Wudker/Weather_station/Hardware/Model/Station/ul.stl

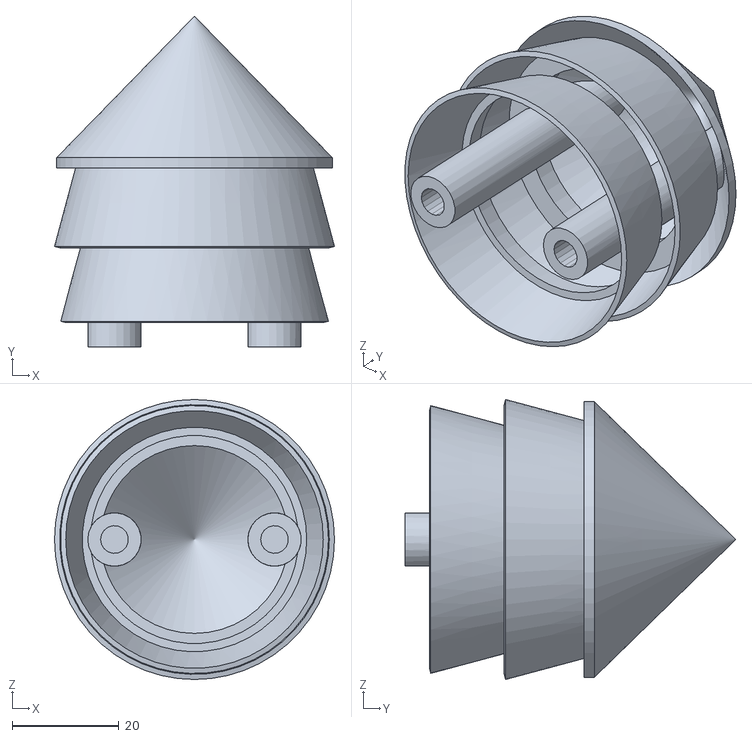
[picture p34: CAD file, 2026-05-24]
Hardware/Model/Station/ul.stl
52.5 x 62.0 x 52.5
