Wudker/Weather_station/Hardware/Model/Station/UL2.stl

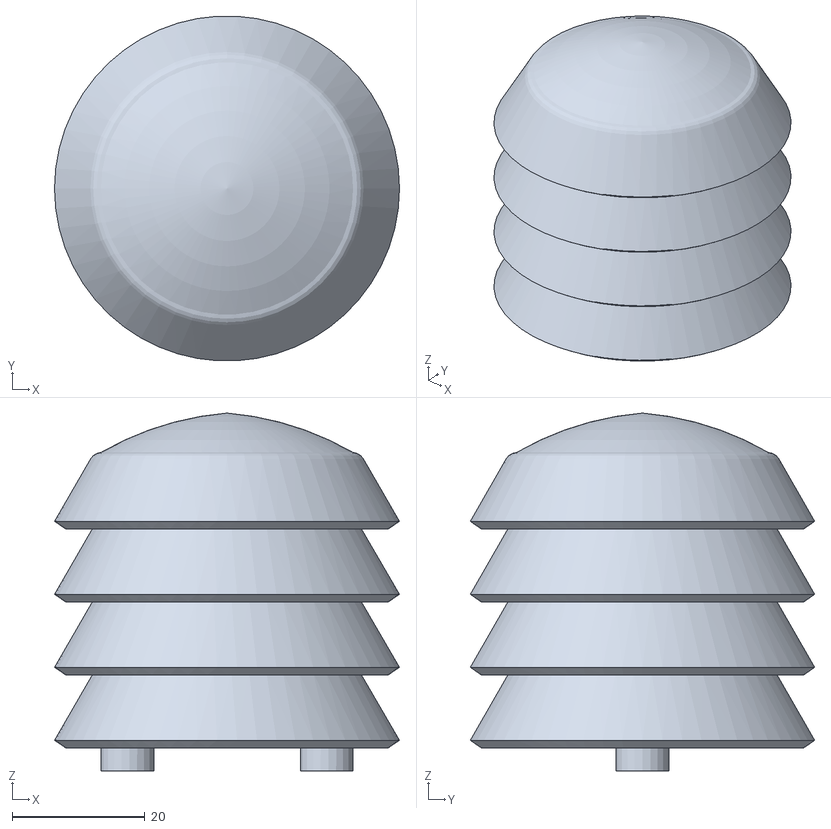
[picture p35: CAD file, 2026-05-24]
Hardware/Model/Station/UL2.stl
52.0 x 51.9 x 53.9
