Wudker/Weather_station/Software/Code/V3/Odbiornik/PogodynkaRxTypes.h

#pragma once

struct Dane_ESP{
float Temperature;
float Humility;
float Pressure;
float Wind_speed;
float Rain;
int Day;
int Month;
int Year;
int Hour;
int Minute;
float Battery_level;
float Sun_level;
};
