Wudker/Weather_station/Software/Code/V3/Odbiornik/Secret_keys.h

#pragma once

#include <stdint.h>

extern const char* ssid;
extern const char* password;
extern const char* mqttBroker_ip;
extern const uint16_t mqttBroker_port;
extern const char* mqttUsername;
extern const char* mqttPassword;
